maz-1/CSPS_ATX_Backplate/Arduino/KCORES_Link_V1/include/FreeMonoBold7pt7b.h

const uint8_t FreeMonoBold7pt7bBitmaps[] PROGMEM = {
  0x00, 0xFF, 0xF1, 0xC0, 0xD9, 0x99, 0x29, 0xA6, 0xBF, 0x69, 0xAF, 0xD6,
  0x59, 0x60, 0x31, 0xF4, 0xD0, 0x78, 0x3C, 0x7F, 0x30, 0xC1, 0x00, 0xF2,
  0x47, 0x07, 0xF8, 0x92, 0x47, 0x01, 0xE4, 0x18, 0x6F, 0xFD, 0x9F, 0xF4,
  0x0F, 0x69, 0x24, 0xC9, 0x80, 0x93, 0x26, 0xDA, 0x5A, 0x00, 0x00, 0xCF,
  0xDE, 0x39, 0xA0, 0x10, 0x60, 0xC7, 0xEF, 0xE6, 0x0C, 0x18, 0x6B, 0x40,
  0xFD, 0xFC, 0x70, 0x04, 0x10, 0xC2, 0x18, 0x43, 0x08, 0x61, 0x0C, 0x00,
  0x31, 0xEC, 0xF1, 0xC7, 0x1C, 0x53, 0x78, 0x13, 0xC3, 0x0C, 0x30, 0xC3,
  0x0C, 0xFC, 0x33, 0xE8, 0xC3, 0x18, 0xC6, 0x31, 0xFC, 0x33, 0xF0, 0x43,
  0x38, 0x30, 0x63, 0xF8, 0x18, 0x63, 0x8A, 0x4B, 0x2F, 0xC2, 0x3C, 0x79,
  0xF4, 0x1E, 0x7C, 0x10, 0x63, 0xF8, 0x1C, 0xF6, 0x10, 0xFF, 0x14, 0x59,
  0x3C, 0xFF, 0xF8, 0xC2, 0x08, 0x61, 0x04, 0x30, 0x31, 0xFC, 0x73, 0x79,
  0x3C, 0x73, 0x78, 0x39, 0xF4, 0x51, 0x7C, 0xD0, 0xC6, 0xF0, 0xF0, 0x70,
  0x6C, 0x06, 0xB4, 0x04, 0x77, 0x38, 0x38, 0x30, 0xFF, 0xF8, 0x07, 0xF0,
  0x81, 0xC0, 0xE0, 0xE7, 0x18, 0x00, 0x7B, 0x30, 0x43, 0x38, 0x41, 0x0C,
  0x01, 0xEC, 0xE1, 0xBE, 0x9A, 0x67, 0x81, 0x07, 0x80, 0x78, 0x0C, 0x0F,
  0x04, 0x87, 0xE3, 0xF1, 0x0D, 0xCE, 0xFC, 0x66, 0x62, 0x7E, 0x7E, 0x63,
  0x63, 0xFE, 0x3E, 0x63, 0x42, 0xC0, 0xC0, 0x40, 0x63, 0x3E, 0xFC, 0x46,
  0x42, 0x43, 0x43, 0x42, 0x46, 0xFC, 0xFE, 0x62, 0x6A, 0x78, 0x78, 0x6A,
  0x63, 0xFF, 0xFF, 0x63, 0x6A, 0x78, 0x78, 0x68, 0x60, 0xF8, 0x3F, 0x63,
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
  {   218,   8,   8,   8,    0,   -7 },   // 0x46 'F'
  {   226,   8,   8,   8,    0,   -7 },   // 0x47 'G'
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

const GFXfont FreeMonoBold7pt7b PROGMEM = {
  (uint8_t  *)FreeMonoBold7pt7bBitmaps,
  (GFXglyph *)FreeMonoBold7pt7bGlyphs,
  0x20, 0x7E, 22 };

// Approx. 1284 bytes
