maz-1/CSPS_ATX_Backplate/Arduino/KCORES_Link_V1/include/SourceHanMono_Regular7pt7b.h

const uint8_t SourceHanMono_Regular7pt7bBitmaps[] PROGMEM = {
  0x00, 0x6D, 0xB6, 0xDB, 0x01, 0xB0, 0xCF, 0x3C, 0xF3, 0xCC, 0x00, 0x24, 
  0x48, 0x97, 0xF4, 0x48, 0x91, 0x7F, 0x48, 0x91, 0x22, 0x40, 0x08, 0x08, 
  0x3E, 0x63, 0x40, 0x60, 0x38, 0x0E, 0x03, 0x01, 0x43, 0x7E, 0x08, 0x08, 
  0x08, 0x60, 0x48, 0x24, 0x32, 0x29, 0x23, 0x20, 0x2C, 0x29, 0x24, 0xA2, 
  0x61, 0x20, 0x60, 0x18, 0x12, 0x09, 0x04, 0x82, 0x80, 0x81, 0xC7, 0x92, 
  0x8F, 0x43, 0x33, 0xCF, 0x30, 0xFF, 0xC0, 0x12, 0x64, 0xC8, 0x88, 0x88, 
  0x84, 0x46, 0x21, 0x84, 0x62, 0x21, 0x11, 0x11, 0x12, 0x26, 0xC8, 0x10, 
  0x23, 0x5B, 0xE1, 0x07, 0x1B, 0x22, 0x10, 0x20, 0x47, 0xF1, 0x02, 0x04, 
  0x08, 0xDF, 0xB7, 0x80, 0xFE, 0xFF, 0x80, 0x02, 0x04, 0x18, 0x20, 0xC1, 
  0x06, 0x08, 0x30, 0x41, 0x82, 0x0C, 0x10, 0x20, 0x00, 0x3C, 0x66, 0x42, 
  0x81, 0x81, 0x99, 0x99, 0x81, 0x81, 0x42, 0x66, 0x3C, 0x30, 0x70, 0x10, 
  0x10, 0x10, 0x10, 0x10, 0x10, 0x10, 0x10, 0x10, 0xFF, 0x78, 0xC4, 0x02, 
  0x02, 0x02, 0x06, 0x04, 0x08, 0x18, 0x30, 0x60, 0xFF, 0x7C, 0x46, 0x02, 
  0x02, 0x04, 0x38, 0x06, 0x01, 0x01, 0x01, 0xC2, 0x7C, 0x06, 0x03, 0x02, 
  0x83, 0x41, 0x21, 0x11, 0x89, 0x84, 0xFF, 0x81, 0x00, 0x80, 0x40, 0x7F, 
  0x60, 0x40, 0x40, 0x7C, 0x42, 0x01, 0x01, 0x01, 0x01, 0xC2, 0x7C, 0x1E, 
  0x61, 0x40, 0x80, 0x80, 0xBC, 0xC3, 0x81, 0x81, 0x41, 0x62, 0x3C, 0xFF, 
  0x02, 0x06, 0x04, 0x08, 0x08, 0x08, 0x10, 0x10, 0x10, 0x10, 0x10, 0x3C, 
  0x66, 0x42, 0x42, 0x62, 0x3C, 0x6E, 0x83, 0x81, 0x81, 0x43, 0x3C, 0x3C, 
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
  {   366,   8,  12,  10,    1,  -11 },   // 0x47 'G'
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
};

const GFXfont SourceHanMono_Regular7pt7b PROGMEM = {
  (uint8_t  *)SourceHanMono_Regular7pt7bBitmaps,     
  (GFXglyph *)SourceHanMono_Regular7pt7bGlyphs, 0x20, 0x7E,    16 };

// Approx. 1651 bytes
