maz-1/CSPS_ATX_Backplate/Arduino/KCORES_Link_V1/include/ArialNarrow7pt7b.h

const uint8_t ArialNarrow7pt7bBitmaps[] PROGMEM = {
  0x00, 0xFF, 0x40, 0xB6, 0xD0, 0x12, 0x24, 0x97, 0xF2, 0x44, 0xBF, 0xA4, 
  0x48, 0x90, 0x23, 0xAB, 0x4A, 0x38, 0xA5, 0xAD, 0x5C, 0x40, 0x61, 0x24, 
  0x89, 0x22, 0x50, 0x64, 0x02, 0x60, 0xA4, 0x49, 0x12, 0x48, 0x60, 0x30, 
  0x91, 0x22, 0x86, 0x1A, 0xA5, 0x44, 0x8C, 0xEC, 0xF0, 0x29, 0x49, 0x24, 
  0x91, 0x22, 0x89, 0x12, 0x49, 0x25, 0x28, 0x5D, 0x50, 0x21, 0x3E, 0x42, 
  0x00, 0x58, 0xE0, 0x80, 0x24, 0x94, 0x92, 0x90, 0x00, 0x22, 0xA3, 0x18, 
  0xC6, 0x31, 0x51, 0x00, 0x25, 0xD2, 0x49, 0x24, 0x64, 0xA2, 0x10, 0x88, 
  0x88, 0x87, 0xC0, 0x64, 0x82, 0x22, 0x08, 0x31, 0x93, 0x00, 0x08, 0x61, 
  0x8A, 0x29, 0x28, 0xBF, 0x08, 0x20, 0x7A, 0x21, 0xC9, 0x04, 0x31, 0x93, 
  0x00, 0x32, 0x61, 0x0A, 0x6A, 0x31, 0x51, 0x00, 0xF8, 0x44, 0x22, 0x10, 
  0x88, 0x42, 0x00, 0x22, 0xA2, 0xA2, 0x2A, 0x31, 0x51, 0x00, 0x22, 0xA3, 
  0x15, 0x94, 0x21, 0x93, 0x00, 0xF0, 0x3C, 0x00, 0xF0, 0x3D, 0x80, 0x04, 
  0x66, 0x20, 0x60, 0x60, 0x40, 0xFC, 0x00, 0x3F, 0x81, 0x81, 0x81, 0x19, 
  0x88, 0x00, 0x74, 0x62, 0x10, 0x88, 0x84, 0x01, 0x00, 0x1E, 0x08, 0x44, 
  0x0A, 0x75, 0xA3, 0x68, 0x9A, 0x26, 0x89, 0xA6, 0x66, 0xE4, 0x04, 0x82, 
  0x1F, 0x00, 0x10, 0x50, 0xA1, 0x42, 0x88, 0x9F, 0x22, 0x83, 0x04, 0xFA, 
  0x18, 0x61, 0xFA, 0x18, 0x61, 0x87, 0xE0, 0x39, 0x18, 0x60, 0x82, 0x08, 
  0x61, 0x48, 0xC0, 0xF2, 0x28, 0x61, 0x86, 0x18, 0x61, 0x8B, 0xC0, 0xFE, 
  0x08, 0x20, 0xFE, 0x08, 0x20, 0x83, 0xF0, 0xFE, 0x08, 0x20, 0xFA, 0x08, 
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
  {   223,   6,  10,   7,    1,   -9 },   // 0x46 'F'
  {   231,   7,  10,   9,    1,   -9 },   // 0x47 'G'
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
};

const GFXfont ArialNarrow7pt7b PROGMEM = {
  (uint8_t  *)ArialNarrow7pt7bBitmaps,  
  (GFXglyph *)ArialNarrow7pt7bGlyphs, 0x20, 0x7E, 16 };

// Approx. 1245 bytes
