maz-1/CSPS_ATX_Backplate/Arduino/KCORES_Link_V1/include/Digital_7pt7b.h

const uint8_t Digital_7pt7bBitmaps[] PROGMEM = {
  0x00, 0xF0, 0x7A, 0x18, 0x61, 0x84, 0x08, 0x61, 0x86, 0x17, 0x80, 0x7B, 
  0xC0, 0x78, 0x10, 0x41, 0x05, 0xE8, 0x20, 0x82, 0x07, 0x80, 0xF0, 0x42, 
  0x10, 0xF8, 0x21, 0x08, 0x7C, 0x00, 0x02, 0x18, 0x61, 0x85, 0xE0, 0x41, 
  0x04, 0x10, 0x7A, 0x08, 0x20, 0x81, 0xE0, 0x41, 0x04, 0x17, 0x80, 0x7A, 
  0x08, 0x20, 0x81, 0xE8, 0x61, 0x86, 0x17, 0x80, 0xF0, 0x42, 0x10, 0x80, 
  0x21, 0x08, 0x40, 0x00, 0x7A, 0x18, 0x61, 0x85, 0xE8, 0x61, 0x86, 0x17, 
  0x80, 0x7A, 0x18, 0x61, 0x85, 0xE0, 0x41, 0x04, 0x17, 0x80, 0xF0, 0x3C, 
  0x00, 0x7A, 0x18, 0x61, 0x85, 0xE8, 0x61, 0x86, 0x10, 0x72, 0x28, 0x61, 
  0x89, 0xC8, 0xA1, 0x86, 0x27, 0x00, 0x7C, 0x21, 0x08, 0x02, 0x10, 0x84, 
  0x1E, 0x00, 0x72, 0x28, 0x61, 0x86, 0x18, 0x61, 0x86, 0x27, 0x00, 0x7C, 
  0x21, 0x08, 0x3E, 0x10, 0x84, 0x1E, 0x00, 0x7C, 0x21, 0x08, 0x3E, 0x10, 
  0x84, 0x00, 0x7A, 0x08, 0x20, 0x80, 0x68, 0x61, 0x86, 0x17, 0x80, 0x86, 
  0x18, 0x61, 0x7A, 0x18, 0x61, 0x84, 0x00, 0x71, 0x08, 0x42, 0x10, 0x84, 
  0x21, 0x1C, 0x00, 0x04, 0x10, 0x41, 0x02, 0x18, 0x61, 0x85, 0xE0, 0x82, 
  0x08, 0x20, 0x02, 0x08, 0x20, 0x81, 0xE0, 0x86, 0x1C, 0xFF, 0xB6, 0x18, 
  0x61, 0x86, 0x10, 0x87, 0x1C, 0x69, 0xA6, 0x59, 0x63, 0x8E, 0x10, 0x31, 
  0x28, 0x61, 0x86, 0x18, 0x61, 0x85, 0x23, 0x00, 0x7A, 0x18, 0x61, 0x85, 
  0xE8, 0x20, 0x82, 0x00, 0x7A, 0x18, 0x61, 0x85, 0xEA, 0x24, 0x8A, 0x10, 
  0x7A, 0x18, 0x60, 0x81, 0xE0, 0x41, 0x86, 0x17, 0x80, 0x7C, 0x21, 0x08, 
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
  {   127,   5,  10,   8,    1,  -11 },   // 0x46 'F'
  {   134,   6,  11,   8,    1,  -11 },   // 0x47 'G'
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
};

const GFXfont Digital_7pt7b PROGMEM = {
  (uint8_t  *)Digital_7pt7bBitmaps,                       
  (GFXglyph *)Digital_7pt7bGlyphs, 0x20, 0x75,   16 };

// Approx. 1651 bytes
