maz-1/CSPS_ATX_Backplate/Arduino/KCORES_Link_V1/extra.py

Import("env")

#
# Dump build environment (for debug)
# print(env.Dump())
#

env.Append(
  LINKFLAGS=[
    "-flto"
  ]
)
env.Append(
  CCFLAGS=[
    "-flto"
  ]
)
env.Append(
  CXXFLAGS=[
    "-flto"
  ]
)
